kuro68k/Superplay/Joystick/joystick/autofire.c

/*
 * autofire.c
 *
 */

#include <avr/io.h>
#include <avr/interrupt.h>
#include <avr/pgmspace.h>
#include <stdlib.h>
#include <string.h>
#include "global.h"
#include "hw_misc.h"
#include "config.h"
#include "report.h"
#include "keys.h"
#include "autofire.h"


const __flash uint16_t prescalers_lut[] = { 1, 2, 4, 8, 64, 256, 1024 };
const __flash uint8_t clksel_lut[] = {	TC_CLKSEL_DIV1_gc, TC_CLKSEL_DIV2_gc, TC_CLKSEL_DIV4_gc,
										TC_CLKSEL_DIV8_gc, TC_CLKSEL_DIV64_gc, TC_CLKSEL_DIV256_gc,
										TC_CLKSEL_DIV1024_gc };



uint8_t	af_high_counters[16];
uint8_t af_low_counters[16];
uint8_t	af_high_duty = 3;			// 50% duty cycle
uint8_t af_low_duty = 3;
uint8_t volatile af_high_count_AT = 0;	// !! ATOMIC !!
uint8_t volatile af_low_count_AT = 0;	// !! ATOMIC !!

uint16_t	af_map = 0xFFFF;		// autofire state for each button
uint16_t	AF_high_map = 0;
uint16_t	AF_low_map = 0;


/**************************************************************************************************
** Find the best timer settings for a given frequency. Returns true if a usable (but possibly
** very inaccurate) setting is found.
*/
bool af_calc_timer(float freq_hz, uint8_t *clksel, uint16_t *period)
{
	uint32_t	cycles;
	uint32_t	per;
	uint32_t	lowest_error = UINT32_MAX;
	bool		found = false;

	cycles = F_CPU / freq_hz;

	// find best prescaler
	for (uint8_t i = 0; i < (sizeof(prescalers_lut) / sizeof(uint16_t)); i++)
	{
		per = cycles / prescalers_lut[i];
		per--;
		if (per > 0xFFFF)	// unusable
			continue;

		uint32_t error;
		error = abs((int32_t)cycles - (int32_t)((per + 1) * prescalers_lut[i]));
		if (error < lowest_error)
		{
			lowest_error = error;
			*clksel = clksel_lut[i];
			*period = per;
			found = true;
		}
	}

	return found;
}

/**************************************************************************************************
** Set up autofire timers
*/
void AF_init(void)
{
	memset(af_high_counters, AF_CLKMUL, sizeof(af_high_counters));
	memset(af_low_counters, AF_CLKMUL, sizeof(af_low_counters));

	uint16_t	per = AF1_PER;
	uint8_t		clksel = AF1_CLKSEL;
	float		freq_hz;

	freq_hz = settings->af_high_hz;
	if (freq_hz < 1) freq_hz = 1;
	freq_hz *= AF_CLKMUL;				// timer runs AF_CLKMUL times faster than autofire
	if (!af_calc_timer(freq_hz, &clksel, &per))
	{
		clksel = AF1_CLKSEL;
		per = AF1_PER;
	}

	AF_TC1.CTRLA = 0;
	AF_TC1.CTRLB = 0;
	AF_TC1.CTRLC = 0;
	AF_TC1.CTRLD = 0;
	AF_TC1.CTRLE = 0;
	AF_TC1.INTCTRLA = TC_OVFINTLVL_LO_gc;
	AF_TC1.INTCTRLB = 0;
	AF_TC1.CNT = 0;
	AF_TC1.PER = per;
	AF_TC1.CTRLA = clksel;

	freq_hz = settings->af_low_hz;
	if (freq_hz < 1) freq_hz = 1;
	freq_hz *= AF_CLKMUL;
	if (!af_calc_timer(freq_hz, &clksel, &per))
	{
		clksel = AF2_CLKSEL;
		per = AF2_PER;
	}

	AF_TC2.CTRLA = 0;
	AF_TC2.CTRLB = 0;
	AF_TC2.CTRLC = 0;
	AF_TC2.CTRLD = 0;
	AF_TC2.CTRLE = 0;
	AF_TC2.INTCTRLA = TC_OVFINTLVL_LO_gc;
	AF_TC2.INTCTRLB = 0;
	AF_TC2.CNT = 0;
	AF_TC2.PER = per;
	AF_TC2.CTRLA = clksel;

	af_high_duty = (float)settings->af_high_duty_pc * (AF_CLKMUL / 100.0);
	af_low_duty = (float)settings->af_low_duty_pc * (AF_CLKMUL / 100.0);
}

/**************************************************************************************************
** Timer overflow interrupt handlers
*/
ISR(AF_TC1_OVF_vect)
{
	af_high_count_AT++;
}

ISR(AF_TC2_OVF_vect)
{
	af_low_count_AT++;
}

/**************************************************************************************************
** Apply autofire to selected buttons
*/
void AF_apply(void)
{
	uint8_t		i;
	uint8_t		af_high_count, af_low_count;


	cli();
	af_high_count = af_high_count_AT;
	af_low_count = af_low_count_AT;
	sei();


	uint8_t high_temp = af_high_count + 1;
	uint8_t low_temp = af_low_count + 1;
	for (i = 0; i < 16; i++)
	{
		if (!input_matrix[LBUTTON1 + i])		// button not pressed
		{
			af_high_counters[i] = high_temp;	// reset so button engages instantly when pressed
			af_low_counters[i] = low_temp;
		}

		if (input_matrix[LAF_HIGH_1 + i] &&
			(((af_high_count - af_high_counters[i]) & AF_CLKMUL_MASK) > af_high_duty) )
			input_matrix[LBUTTON1 + i] = 0;		// force off to modulate fire button

		if (input_matrix[LAF_LOW_1 + i] &&
			(((af_low_count - af_low_counters[i]) & AF_CLKMUL_MASK) > af_low_duty) )
			input_matrix[LBUTTON1 + i] = 0;		// force off to modulate fire button
	}

	//if (af_low_count & 0b100) input_matrix[LBUTTON1] = 1;
}
