kuro68k/Superplay/Receiver/ReceiverAC/ReceiverAC/atari.h

/*
 * atari.h
 *
 */


#ifndef ATARI_H_
#define ATARI_H_


#define AC_PORT					PORTA
#define AC_JOY_UP_PIN_bm		PIN0_bm
#define AC_JOY_DOWN_PIN_bm		PIN1_bm
#define AC_JOY_LEFT_PIN_bm		PIN2_bm
#define AC_JOY_RIGHT_PIN_bm		PIN3_bm
#define AC_JOY_B1_PIN_bm		PIN4_bm
#define AC_JOY_B2_PIN_bm		PIN5_bm

#define SELECT_PORT				PORTC
#define SELECT_PIN_bm			PIN2_bm

#define DIR_PORT				PORTD
#define DIR_PIN_bm				PIN7_bm


extern void AC_init(void);
extern void AC_update(void);

// atari_asm.S
extern void AT_set_output(void);


#endif /* ATARI_H_ */
