kuro68k/Superplay/Joystick/joystick/hw_misc.h

/*
 * hw_misc.h
 *
 * Created: 18/12/2014 21:22:30
 *  Author: Paul Qureshi
 */


#ifndef HW_MISC_H_
#define HW_MISC_H_



#define DEBUG_RX_PIN_bm			PIN6_bm
#define DEBUG_TX_PIN_bm			PIN7_bm



/**************************************************************************************************
** Macros
*/

// port settings
#define DISABLE_DIGITAL_INPUT(A)	A = (A & ~PORT_ISC_gm) | PORT_ISC_INPUT_DISABLE_gc
#define ENABLE_PULLUP(A)			A = (A & ~PORT_OPC_gm) | PORT_OPC_PULLUP_gc
#define ENABLE_PULLDOWN(A)			A = (A & ~PORT_OPC_gm) | PORT_OPC_PULLDOWN_gc

// wait for NVM to wake up for reading the signature row
#define HW_wait_for_sig_row()	do {} while ((NVM.STATUS & NVM_NVMBUSY_bm) == NVM_NVMBUSY_bm);



/**************************************************************************************************
** External variables and functions
*/

extern uint8_t	HW_last_reset_status;


extern void		HW_init(void);
extern void		HW_reset_rtc(void);
extern void		HW_CCPWrite(volatile uint8_t *address, uint8_t value)		__attribute__((nonnull));



#endif /* HW_MISC_H_ */
