kuro68k/Superplay/Receiver/ReceiverAC/ReceiverAC/hw_misc.h

/*
 * hw_misc.h
 *
 */


#ifndef HW_MISC_H_
#define HW_MISC_H_


/**************************************************************************************************
* I/O pins
*/

#define LED_PORT				PORTD
#define LED_PIN_bm				PIN4_bm


/**************************************************************************************************
* Macros
*/

// port settings
#define DISABLE_DIGITAL_INPUT(A)	A = (A & ~PORT_ISC_gm) | PORT_ISC_INPUT_DISABLE_gc
#define ENABLE_PULLUP(A)			A = (A & ~PORT_OPC_gm) | PORT_OPC_PULLUP_gc
#define ENABLE_PULLDOWN(A)			A = (A & ~PORT_OPC_gm) | PORT_OPC_PULLDOWN_gc
#define ENABLE_TOTEM(A)				A = (A & ~PORT_OPC_gm) | PORT_OPC_TOTEM_gc

// Watchdog timer
#define WATCHDOG_ON					do {	while (WDT.STATUS & WDT_SYNCBUSY_bm);									\
											WDR();																	\
											HW_CCPWrite(&WDT.CTRL, WDT_PER_8KCLK_gc | WDT_ENABLE_bm | WDT_CEN_bm);	\
									} while(0)

#define WATCHDOG_OFF				do {	while (WDT.STATUS & WDT_SYNCBUSY_bm);									\
											HW_CCPWrite(&WDT.CTRL, WDT_CEN_bm);										\
									} while(0)

#define WDR()						asm("wdr")

#define NOP()						asm("nop")


/**************************************************************************************************
* Public functions and variables
*/

// assembler functions in hw_nvm.S
extern uint8_t	HW_read_fuse_byte(uint8_t index);
extern uint8_t	HW_read_signature_byte(uint8_t index);
extern uint8_t	HW_read_user_signature_byte(uint16_t index);
extern void		HW_WaitForSPM(void);
extern uint32_t	HW_application_crc(void);
extern uint32_t	HW_boot_crc(void);

// hw_misc.c
extern void		HW_init(void);
extern void		HW_CCPWrite(volatile uint8_t *address, uint8_t value);
extern uint16_t	HW_crc16(const void *buffer, uint8_t length);


#endif /* HW_MISC_H_ */
