kuro68k/Superplay/Receiver/ReceiverAC/ReceiverAC/version.h

/*
 * version.h
 *
 */


#ifndef VERSION_H_
#define VERSION_H_


#define VERSION_MAJOR	0
#define VERSION_MINOR	1


#define BUILD_SIMPLE
//#define BUILD_PC_ENGINE
//#define BUILD_SEGA



#endif /* VERSION_H_ */
